Iskandar152/Joystick-Controlled-Quade/MSP432 UART Communication/uart_pc_echo_12mhz_brclk.c

/* DriverLib Includes */
#include <ti/devices/msp432p4xx/driverlib/driverlib.h>

#include <ti/devices/msp432p4xx/inc/msp.h>

/* Standard Includes */
#include <stdint.h>
#include <stdbool.h>

//![Simple UART Config]
/* UART Configuration Parameter. These are the configuration parameters to
 * make the eUSCI A UART module to operate with a 9600 baud rate. These
 * values were calculated using the online calculator that TI provides
 * at:
 *http://software-dl.ti.com/msp430/msp430_public_sw/mcu/msp430/MSP430BaudRateConverter/index.html
 */
const eUSCI_UART_ConfigV1 uartConfig =
{
        EUSCI_A_UART_CLOCKSOURCE_SMCLK,          // SMCLK Clock Source
        78,                                     // BRDIV = 78
        2,                                       // UCxBRF = 2
        0,                                       // UCxBRS = 0
        EUSCI_A_UART_NO_PARITY,                  // No Parity
        EUSCI_A_UART_LSB_FIRST,                  // LSB First
        EUSCI_A_UART_ONE_STOP_BIT,               // One stop bit
        EUSCI_A_UART_MODE,                       // UART mode
        EUSCI_A_UART_OVERSAMPLING_BAUDRATE_GENERATION,  // Oversampling
        EUSCI_A_UART_8_BIT_LEN                  // 8 bit data length
};
//![Simple UART Config]

int main(void)
{
    /* Halting WDT  */
    MAP_WDT_A_holdTimer();

    /* Selecting P1.2 and P1.3 in UART mode */
    MAP_GPIO_setAsPeripheralModuleFunctionInputPin(GPIO_PORT_P3,
            GPIO_PIN2 | GPIO_PIN3, GPIO_PRIMARY_MODULE_FUNCTION);

    /* Setting DCO to 12MHz */
    CS_setDCOCenteredFrequency(CS_DCO_FREQUENCY_12);

    //![Simple UART Example]
    /* Configuring UART Module */
    MAP_UART_initModule(EUSCI_A2_BASE, &uartConfig);

    /* Enable UART module */
    MAP_UART_enableModule(EUSCI_A2_BASE);

    /* Enabling interrupts */
    MAP_UART_enableInterrupt(EUSCI_A2_BASE, EUSCI_A_UART_RECEIVE_INTERRUPT);
    MAP_Interrupt_enableInterrupt(INT_EUSCIA2);
    MAP_Interrupt_enableSleepOnIsrExit();
    MAP_Interrupt_enableMaster();   
    //![Simple UART Example]

    while(1)
    {
        MAP_PCM_gotoLPM0();
    }
}

void EUSCIA2_IRQHandler(void)
{
    uint32_t status = MAP_UART_getEnabledInterruptStatus(EUSCI_A2_BASE);

    if(status & EUSCI_A_UART_RECEIVE_INTERRUPT_FLAG)
    {
        MAP_UART_transmitData(EUSCI_A2_BASE, MAP_UART_receiveData(EUSCI_A2_BASE));
    }

}
